russeree/nyan-keys-hardware/board_files/nyan_keys_v09a/nyan_keys.kicad_sch

## KiCad design board_files/nyan_keys_v09a/nyan_keys.kicad_sch (2023-12-11)

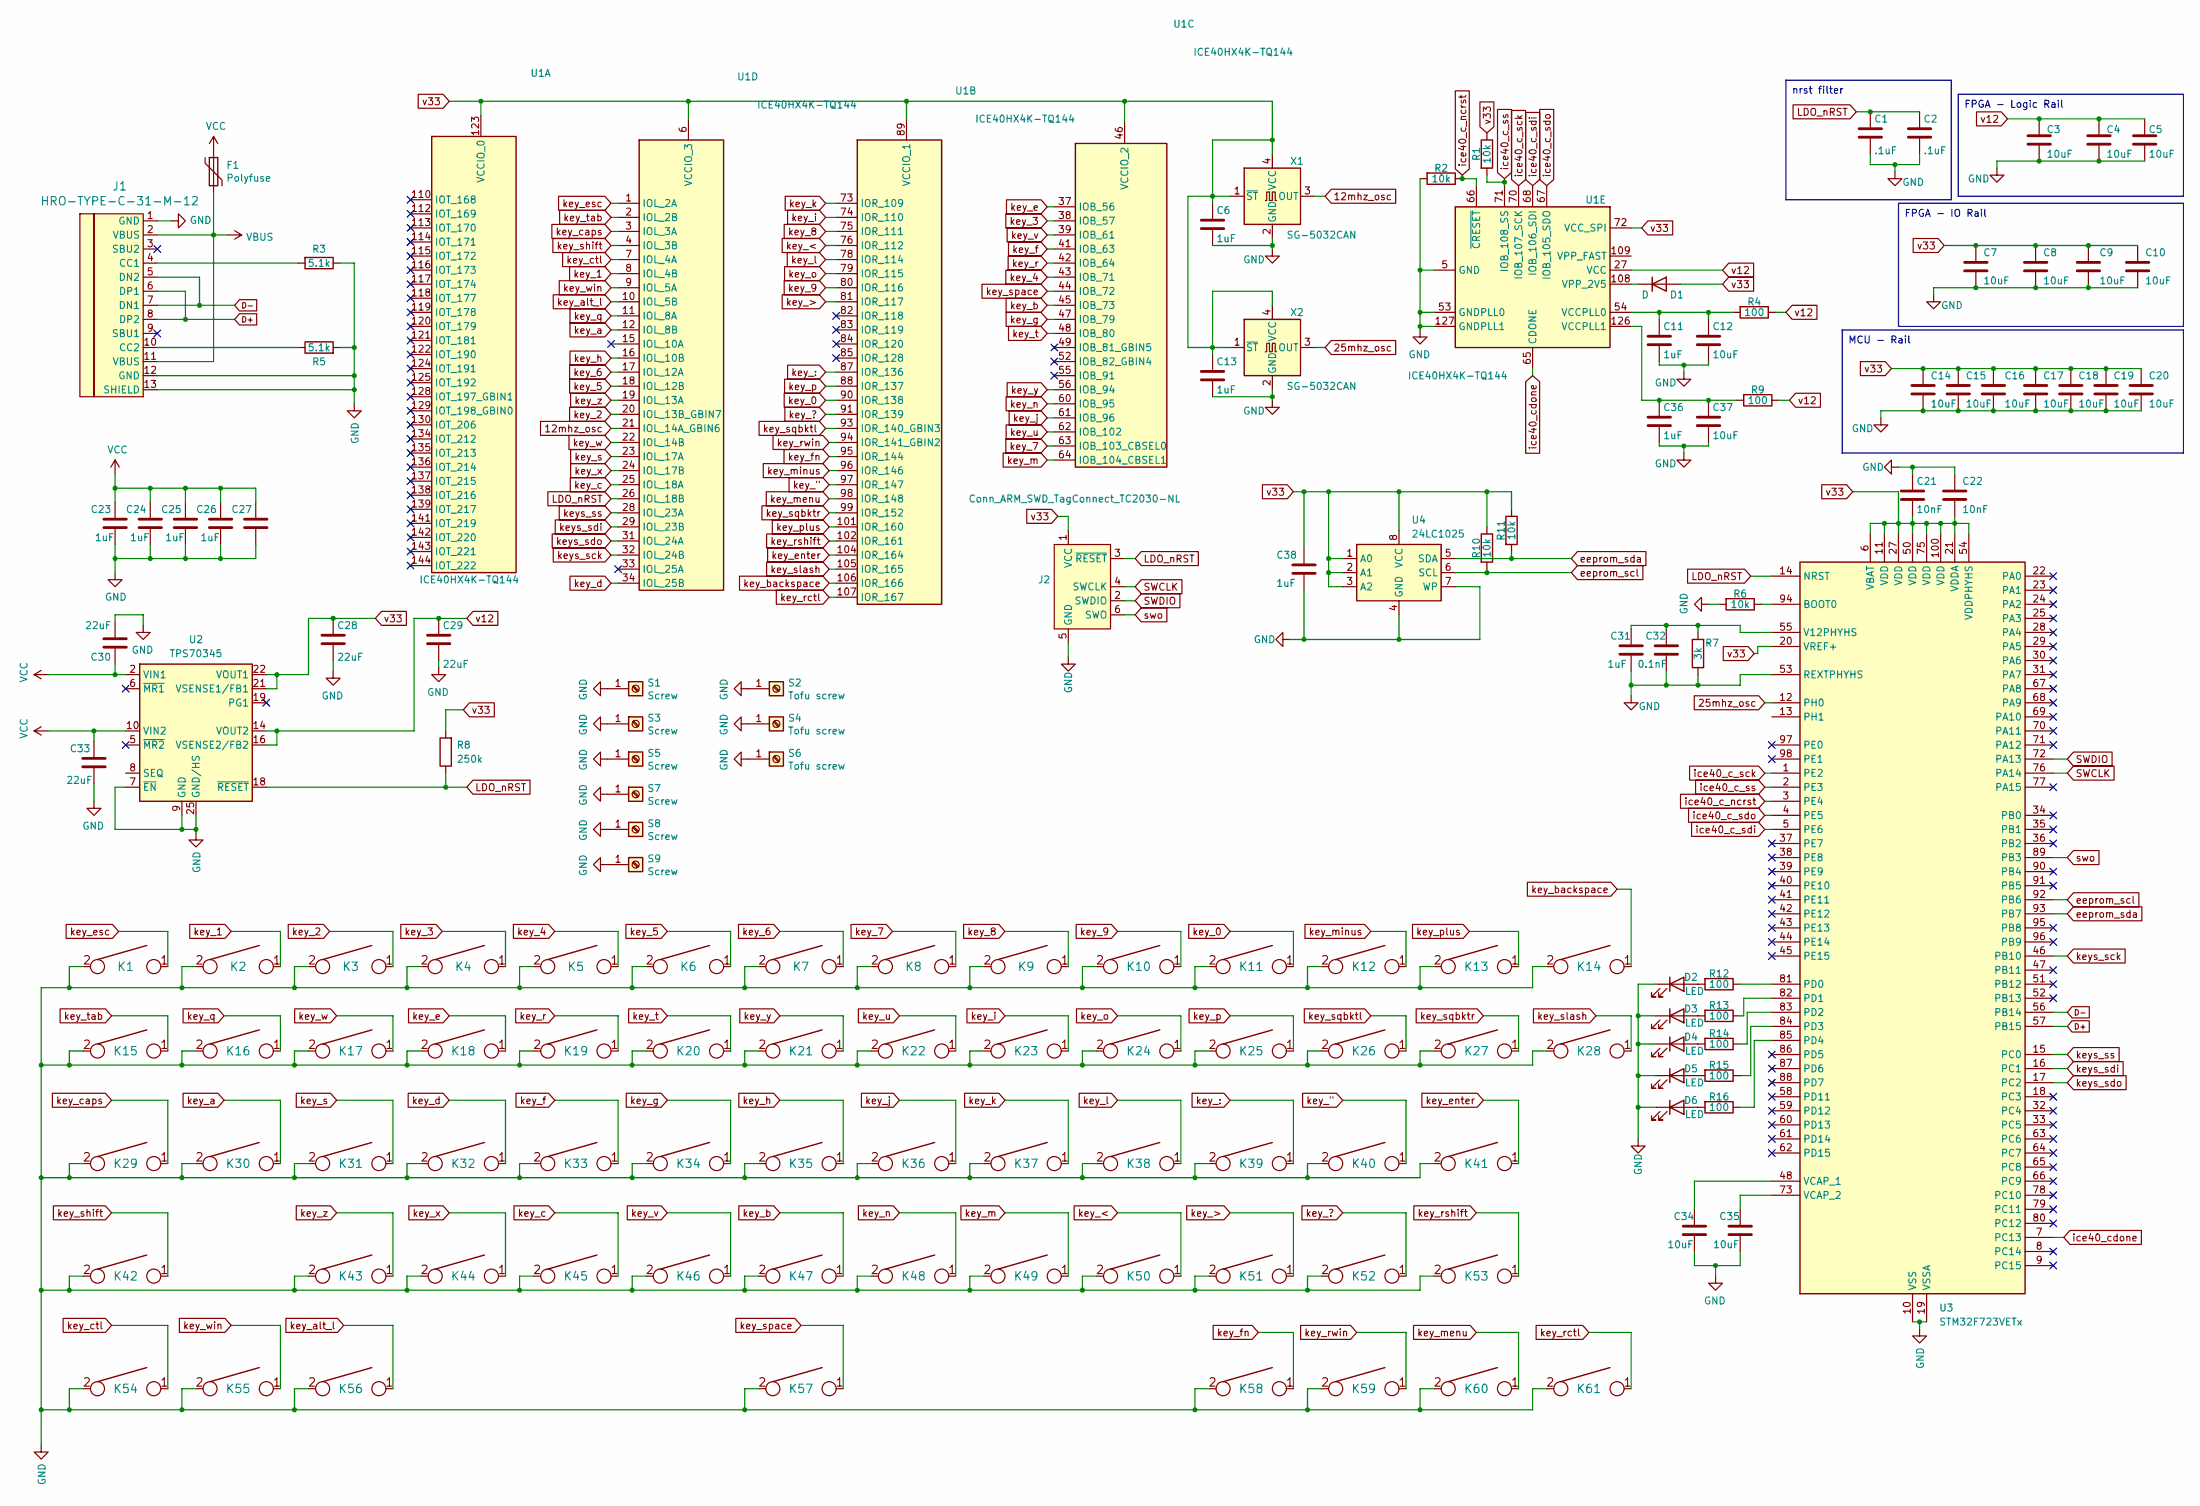
[picture p17: schematic nyan_keys.kicad_sch]

Parts:
C1, C2: .1uF; C_0402_1005Metric_Pad0.74x0.62mm_HandSolder
C3, C4, C5, C7, C8, C9, C10, C12, C14, C15, C16, C17, C18, C19, C20, C34, C35, C37: 10uF; C_0402_1005Metric_Pad0.74x0.62mm_HandSolder
C6, C11, C13, C23, C24, C25, C26, C31, C36, C38: 1uF; C_0402_1005Metric_Pad0.74x0.62mm_HandSolder
C21, C22: 10nF; C_0402_1005Metric_Pad0.74x0.62mm_HandSolder
C27: 4.7uF; C_0402_1005Metric_Pad0.74x0.62mm_HandSolder
C28, C29: 22uF; C_0402_1005Metric_Pad0.74x0.62mm_HandSolder
C30, C33: 22uF; C_0603_1608Metric_Pad1.08x0.95mm_HandSolder
C32: 0.1nF; C_0402_1005Metric_Pad0.74x0.62mm_HandSolder
D1: D; D_0603_1608Metric_Pad1.05x0.95mm_HandSolder
D2, D3, D4, D5, D6: LED; LED_0603_1608Metric_Pad1.05x0.95mm_HandSolder
F1: Polyfuse; R_0805
J1: HRO-TYPE-C-31-M-12
J2: Conn_ARM_SWD_TagConnect_TC2030-NL; Tag-Connect_TC2030-IDC-NL_2x03_P1.27mm_Vertical
K1, K2, K3, K4, K5, K6, K7, K8, K9, K10, K11, K12, K13, K16, K17, K18, K19, K20, K21, K22, K23, K24, K25, K26, K27, K30, K31, K32, K33, K34, K35, K36, K37, K38, K39, K40, K43, K44, K45, K46, K47, K48, K49, K50, K51, K52: KEYSW; CHERRY_PLATE_100H
K14: KEYSW; CHERRY_PCB_200H
K15, K28: KEYSW; CHERRY_PLATE_150H
K29: KEYSW; CHERRY_PLATE_175H
K41, K42: KEYSW; CHERRY_PCB_225H
K53: KEYSW; CHERRY_PCB_275H
K54, K55, K56, K58, K59, K60, K61: KEYSW; CHERRY_PLATE_125H
K57: KEYSW; CHERRY_PCB_625H_F
R1, R2, R6: 10k; R_0603_1608Metric_Pad0.98x0.95mm_HandSolder
R3, R5: 5.1k; R_0805
R4, R9: 100; R_0603_1608Metric_Pad0.98x0.95mm_HandSolder
R7: 3k; R_0402_1005Metric_Pad0.72x0.64mm_HandSolder
R8: 250k; R_0603_1608Metric_Pad0.98x0.95mm_HandSolder
R10, R11: 10k; R_0402_1005Metric_Pad0.72x0.64mm_HandSolder
R12, R13, R14, R15, R16: 100; R_0402_1005Metric_Pad0.72x0.64mm_HandSolder
S1, S3, S5, S9: Screw; 5.5_5x2.5mm
S2, S4, S6: Tofu screw; 5.5_5x2.5mm
S7, S8: Screw; 10x5_7x2.5mm
U1: ICE40HX4K-TQ144; TQFP-144_20x20mm_P0.5mm
U2: TPS70345; HTSSOP-24-1EP_4.4x7.8mm_P0.65mm_EP3.4x7.8mm_Mask2.4x4.68mm_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
U3: STM32F723VETx; LQFP-100_14x14mm_P0.5mm
U4: 24LC1025; SOIC-8_3.9x4.9mm_Pitch1.27mm
X1, X2: SG-5032CAN; Oscillator_SMD_SeikoEpson_SG8002LB-4Pin_5.0x3.2mm

Connections:
12mhz_osc: U1.21 (IOL_14A_GBIN6), X1.3 (OUT)
25mhz_osc: U3.12 (PH0), X2.3 (OUT)
D+: J1.6 (DP1), J1.8 (DP2), U3.57 (PB15)
D-: J1.5 (DN2), J1.7 (DN1), U3.56 (PB14)
GND: C1.2, C2.2, C3.2, C4.2, C5.2, C6.2, C7.2, C8.2, C9.2, C10.2, C11.2, C12.2, C13.2, C14.2, C15.2, C16.2, C17.2, C18.2, C19.2, C20.2, C21.1, C22.1, C23.1, C24.1, C25.1, C26.1, C27.1, C28.2, C29.2, C30.2, C31.1, C32.1, C33.2, C34.1, C35.1, C36.2, C37.2, C38.2, D2.1 (K), D3.1 (K), D4.1 (K), D5.1 (K), D6.1 (K), J1.1 (GND), J1.12 (GND), J1.13 (SHIELD), J2.5 (GND), K1.2, K2.2, K3.2, K4.2, K5.2, K6.2, K7.2, K8.2, K9.2, K10.2, K11.2, K12.2, K13.2, K14.2, K15.2, K16.2, K17.2, K18.2, K19.2, K20.2, K21.2, K22.2, K23.2, K24.2, K25.2, K26.2, K27.2, K28.2, K29.2, K30.2, K31.2, K32.2, K33.2, K34.2, K35.2, K36.2, K37.2, K38.2, K39.2, K40.2, K41.2, K42.2, K43.2, K44.2, K45.2, K46.2, K47.2, K48.2, K49.2, K50.2, K51.2, K52.2, K53.2, K54.2, K55.2, K56.2, K57.2, K58.2, K59.2, K60.2, K61.2, R2.2, R3.1, R5.2, R6.2, R7.1, S1.1, S2.1, S3.1, S4.1, S5.1, S6.1, S7.1, S8.1, S9.1, U1.5 (GND), U1.13 (GND), U1.14 (GND), U1.53 (GNDPLL0), U1.59 (GND), U1.69 (GND), U1.86 (GND), U1.103 (GND), U1.127 (GNDPLL1), U1.132 (GND), U1.140 (GND), U2.1 (GND/HS), U2.7 (~EN), U2.9 (GND), U2.12 (GND/HS), U2.13 (GND/HS), U2.24 (GND/HS), U2.25 (GND/HS), U3.10 (VSS), U3.19 (VSSA), U3.26 (VSS), U3.49 (VSS), U3.53 (REXTPHYHS), U3.74 (VSS), U3.99 (VSS), U4.4 (GND), U4.7 (WP), X1.2 (GND), X2.2 (GND)
LDO_nRST: C1.1, C2.1, J2.3 (~RESET), R8.1, U1.26 (IOL_18B), U2.18 (~RESET), U3.14 (NRST)
unnamed: C11.1, C12.1, R4.2, U1.54 (VCCPLL0)
unnamed: C31.2, C32.2, R7.2, U3.55 (V12PHYHS)
unnamed: C34.2, U3.48 (VCAP_1)
unnamed: C35.2, U3.73 (VCAP_2)
unnamed: C36.1, C37.1, R9.2, U1.126 (VCCPLL1)
unnamed: D1.1 (K), U1.108 (VPP_2V5)
unnamed: D2.2 (A), R12.2
unnamed: D3.2 (A), R13.2
unnamed: D4.2 (A), R14.2
unnamed: D5.2 (A), R15.2
unnamed: D6.2 (A), R16.2
unnamed: J1.4 (CC1), R3.2
unnamed: J1.10 (CC2), R5.1
unnamed: R6.1, U3.94 (BOOT0)
unnamed: R12.1, U3.81 (PD0)
unnamed: R13.1, U3.82 (PD1)
unnamed: R14.1, U3.83 (PD2)
unnamed: R15.1, U3.84 (PD3)
unnamed: R16.1, U3.85 (PD4)
SWCLK: J2.4 (SWCLK), U3.76 (PA14)
SWDIO: J2.2 (SWDIO), U3.72 (PA13)
VBUS: F1.2, J1.2 (VBUS), J1.11 (VBUS)
VCC: C23.2, C24.2, C25.2, C26.2, C27.2, C30.1, C33.1, F1.1, U2.2 (VIN1), U2.3 (VIN1), U2.10 (VIN2), U2.11 (VIN2)
eeprom_scl: R10.2, U3.92 (PB6), U4.6 (SCL)
eeprom_sda: R11.2, U3.93 (PB7), U4.5 (SDA)
ice40_c_ncrst: R2.1, U1.66 (~CRESET), U3.3 (PE4)
ice40_c_sck: U1.70 (IOB_107_SCK), U3.1 (PE2)
ice40_c_sdi: U1.68 (IOB_106_SDI), U3.5 (PE6)
ice40_c_sdo: U1.67 (IOB_105_SDO), U3.4 (PE5)
ice40_c_ss: R1.2, U1.71 (IOB_108_SS), U3.2 (PE3)
ice40_cdone: U1.65 (CDONE), U3.7 (PC13)
key_0: K11.1, U1.90 (IOR_138)
key_1: K2.1, U1.8 (IOL_4B)
key_2: K3.1, U1.20 (IOL_13B_GBIN7)
key_3: K4.1, U1.38 (IOB_57)
key_4: K5.1, U1.43 (IOB_71)
key_5: K6.1, U1.18 (IOL_12B)
key_6: K7.1, U1.17 (IOL_12A)
key_7: K8.1, U1.63 (IOB_103_CBSEL0)
key_8: K9.1, U1.75 (IOR_111)
key_9: K10.1, U1.80 (IOR_116)
key_": K40.1, U1.97 (IOR_147)
key_:: K39.1, U1.87 (IOR_136)
key_<: K50.1, U1.76 (IOR_112)
key_>: K51.1, U1.81 (IOR_117)
key_?: K52.1, U1.91 (IOR_139)
key_a: K30.1, U1.12 (IOL_8B)
key_alt_l: K56.1, U1.10 (IOL_5B)
key_b: K47.1, U1.45 (IOB_73)
key_backspace: K14.1, U1.106 (IOR_166)
key_c: K45.1, U1.25 (IOL_18A)
key_caps: K29.1, U1.3 (IOL_3A)
key_ctl: K54.1, U1.7 (IOL_4A)
key_d: K32.1, U1.34 (IOL_25B)
key_e: K18.1, U1.37 (IOB_56)
key_enter: K41.1, U1.104 (IOR_164)
key_esc: K1.1, U1.1 (IOL_2A)
key_f: K33.1, U1.41 (IOB_63)
key_fn: K58.1, U1.95 (IOR_144)
key_g: K34.1, U1.47 (IOB_79)
key_h: K35.1, U1.16 (IOL_10B)
key_i: K23.1, U1.74 (IOR_110)
key_j: K36.1, U1.61 (IOB_96)
key_k: K37.1, U1.73 (IOR_109)
key_l: K38.1, U1.78 (IOR_114)
key_m: K49.1, U1.64 (IOB_104_CBSEL1)
key_menu: K60.1, U1.98 (IOR_148)
key_minus: K12.1, U1.96 (IOR_146)
key_n: K48.1, U1.60 (IOB_95)
key_o: K24.1, U1.79 (IOR_115)
key_p: K25.1, U1.88 (IOR_137)
key_plus: K13.1, U1.101 (IOR_160)
key_q: K16.1, U1.11 (IOL_8A)
key_r: K19.1, U1.42 (IOB_64)
key_rctl: K61.1, U1.107 (IOR_167)
key_rshift: K53.1, U1.102 (IOR_161)
key_rwin: K59.1, U1.94 (IOR_141_GBIN2)
key_s: K31.1, U1.23 (IOL_17A)
key_shift: K42.1, U1.4 (IOL_3B)
key_slash: K28.1, U1.105 (IOR_165)
key_space: K57.1, U1.44 (IOB_72)
key_sqbktl: K26.1, U1.93 (IOR_140_GBIN3)
key_sqbktr: K27.1, U1.99 (IOR_152)
key_t: K20.1, U1.48 (IOB_80)
key_tab: K15.1, U1.2 (IOL_2B)
key_u: K22.1, U1.62 (IOB_102)
key_v: K46.1, U1.39 (IOB_61)
key_w: K17.1, U1.22 (IOL_14B)
key_win: K55.1, U1.9 (IOL_5A)
key_x: K44.1, U1.24 (IOL_17B)
key_y: K21.1, U1.56 (IOB_94)
key_z: K43.1, U1.19 (IOL_13A)
keys_sck: U1.32 (IOL_24B), U3.46 (PB10)
keys_sdi: U1.29 (IOL_23B), U3.16 (PC1)
keys_sdo: U1.31 (IOL_24A), U3.17 (PC2)
keys_ss: U1.28 (IOL_23A), U3.15 (PC0)
swo: J2.6 (SWO), U3.89 (PB3)
v12: C3.1, C4.1, C5.1, C29.1, R4.1, R9.1, U1.27 (VCC), U1.40 (VCC), U1.92 (VCC), U1.111 (VCC), U2.14 (VOUT2), U2.15 (VOUT2), U2.16 (VSENSE2/FB2)
v33: C6.1, C7.1, C8.1, C9.1, C10.1, C13.1, C14.1, C15.1, C16.1, C17.1, C18.1, C19.1, C20.1, C21.2, C22.2, C28.1, C38.1, D1.2 (A), J2.1 (VCC), R1.1, R8.2, R10.1, R11.1, U1.6 (VCCIO_3), U1.30 (VCCIO_3), U1.46 (VCCIO_2), U1.57 (VCCIO_2), U1.72 (VCC_SPI), U1.89 (VCCIO_1), U1.100 (VCCIO_1), U1.123 (VCCIO_0), U1.131 (VCCIO_0), U2.21 (VSENSE1/FB1), U2.22 (VOUT1), U2.23 (VOUT1), U3.6 (VBAT), U3.11 (VDD), U3.20 (VREF+), U3.21 (VDDA), U3.27 (VDD), U3.50 (VDD), U3.54 (VDDPHYHS), U3.75 (VDD), U3.100 (VDD), U4.1 (A0), U4.2 (A1), U4.3 (A2), U4.8 (VCC), X1.1 (~ST), X1.4 (VCC), X2.1 (~ST), X2.4 (VCC)

Notes on the sheet:
FPGA - IO Rail
FPGA - Logic Rail
MCU - Rail
nrst filter
